WilliTourt/PixPill/Hardware/PCBs/Imgs/EVK V2/IMG_20260525_212544.jpg

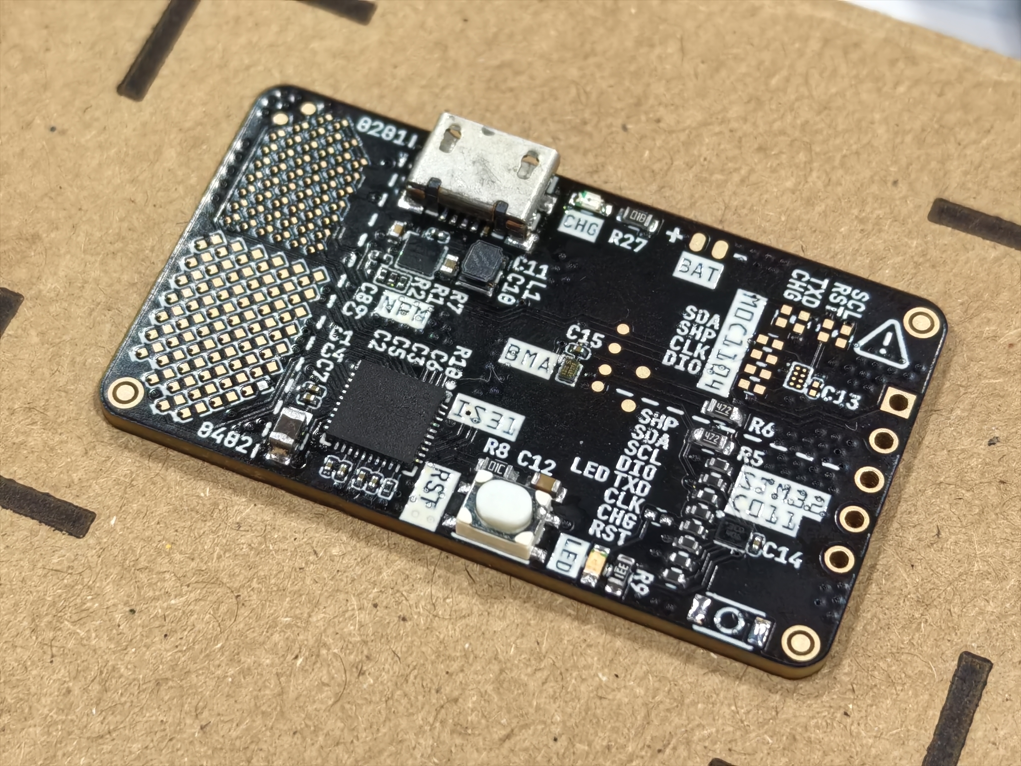
Hardware/PCBs/Imgs/EVK V2/IMG_20260525_212544.jpg
