WilliTourt/PixPill/Hardware/PCBs/Imgs/EVK V2/IMG_20260529_113353.jpg

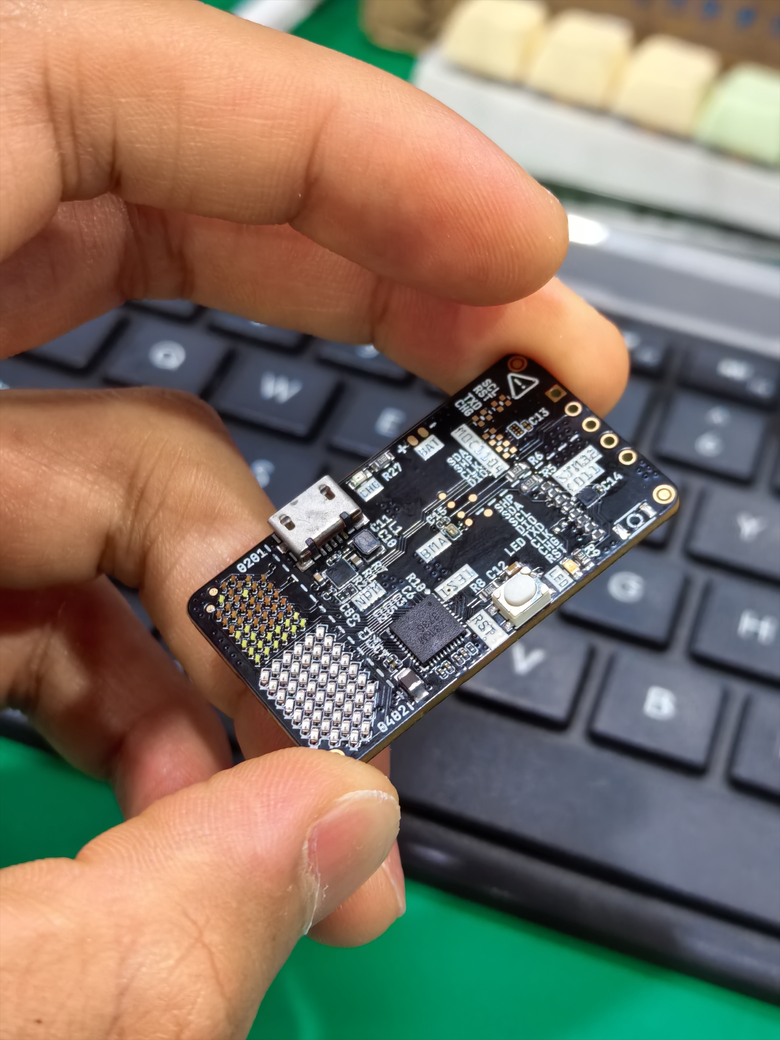
Hardware/PCBs/Imgs/EVK V2/IMG_20260529_113353.jpg
