WilliTourt/PixPill/Hardware/PCBs/Imgs/EVK V2/IMG_20260531_200836.jpg

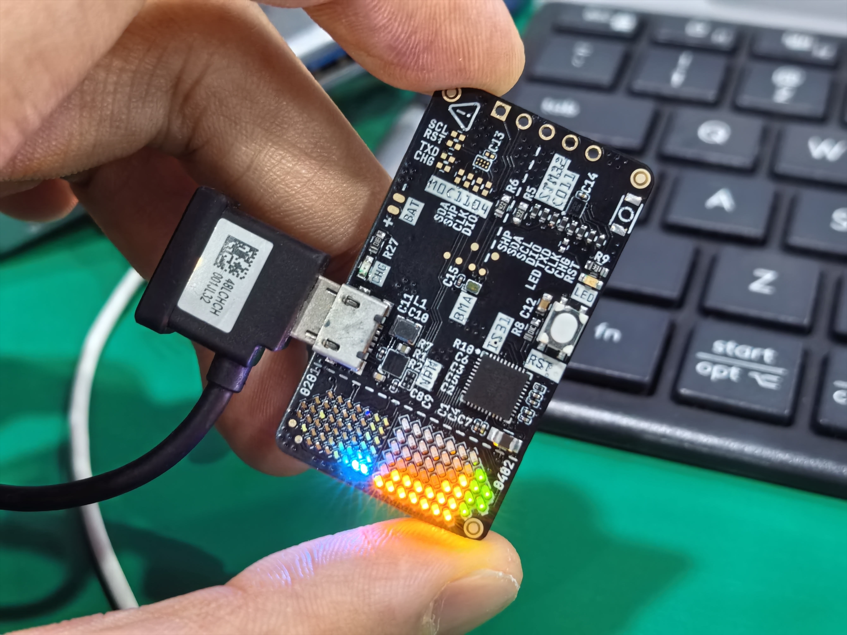
Hardware/PCBs/Imgs/EVK V2/IMG_20260531_200836.jpg
