WilliTourt/PixPill/Hardware/PCBs/Imgs/EVK V2/IMG_20260531_201009.jpg

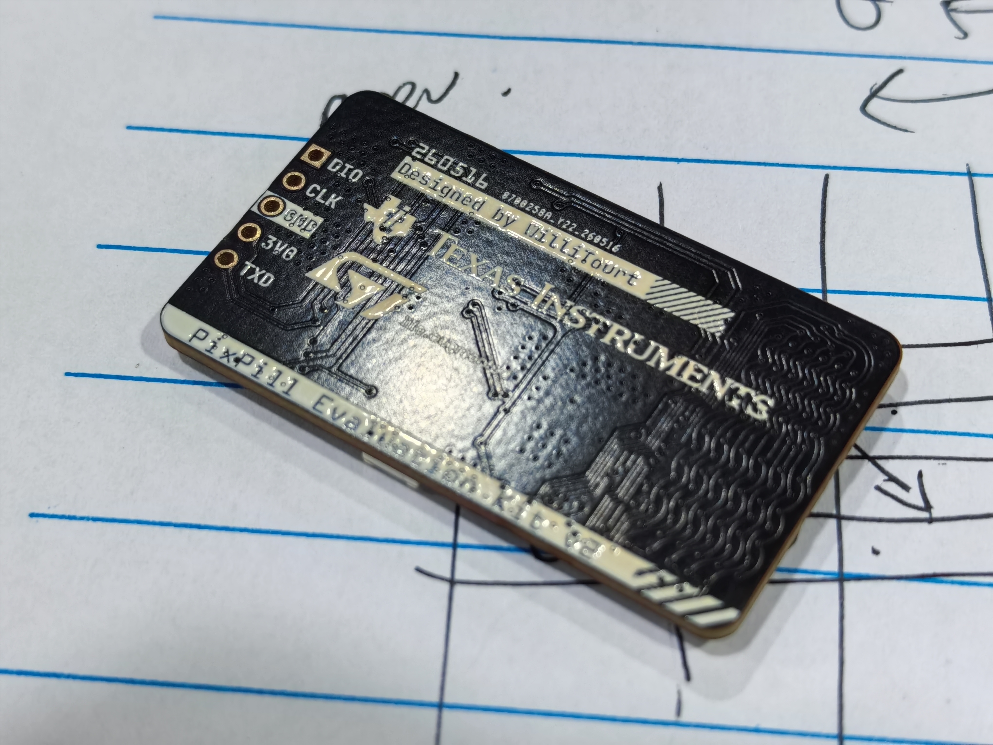
Hardware/PCBs/Imgs/EVK V2/IMG_20260531_201009.jpg
