WilliTourt/PixPill/Hardware/PCBs/Schems and Layout/EVK V2/EVK V2 Bottom.png

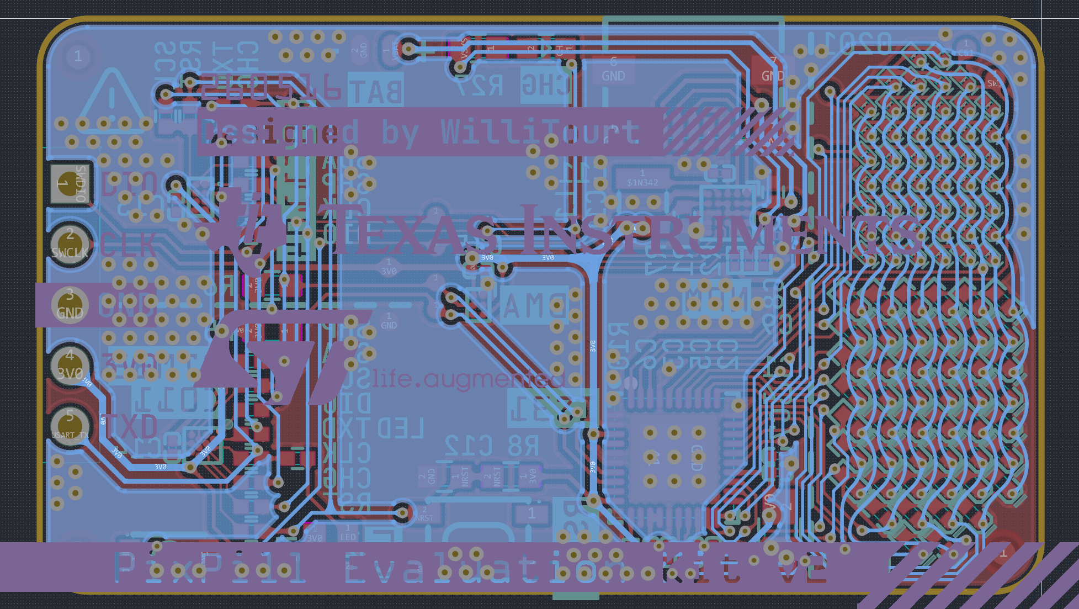
Hardware/PCBs/Schems and Layout/EVK V2/EVK V2 Bottom.png
