WilliTourt/PixPill/Hardware/PCBs/Schems and Layout/EVK V2/IS31.png

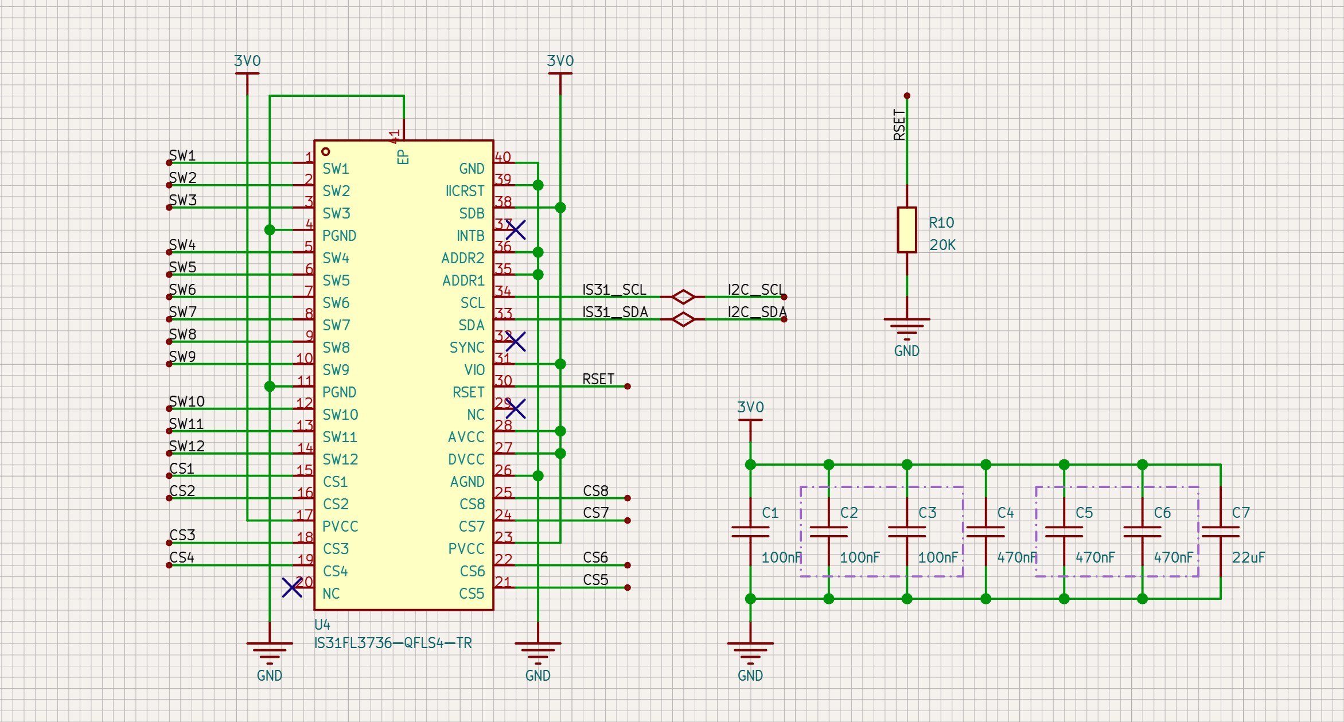
Hardware/PCBs/Schems and Layout/EVK V2/IS31.png
