WilliTourt/PixPill/Hardware/PCBs/Schems and Layout/EVK V2/MCU and BMA.png

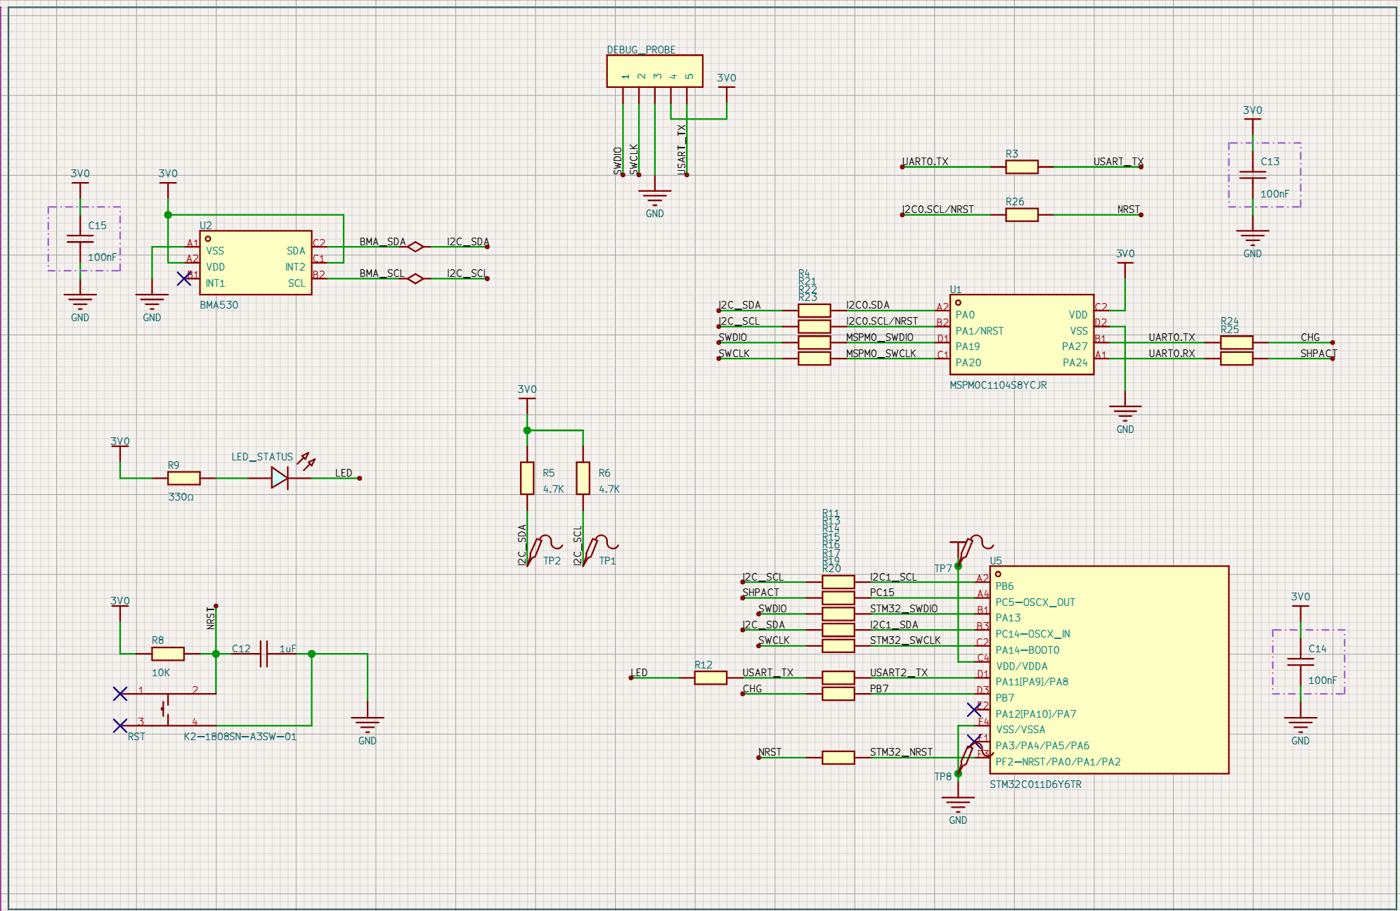
Hardware/PCBs/Schems and Layout/EVK V2/MCU and BMA.png
