WilliTourt/PixPill/Hardware/PCBs/Schems and Layout/Size 000/Size000 Bottom.png

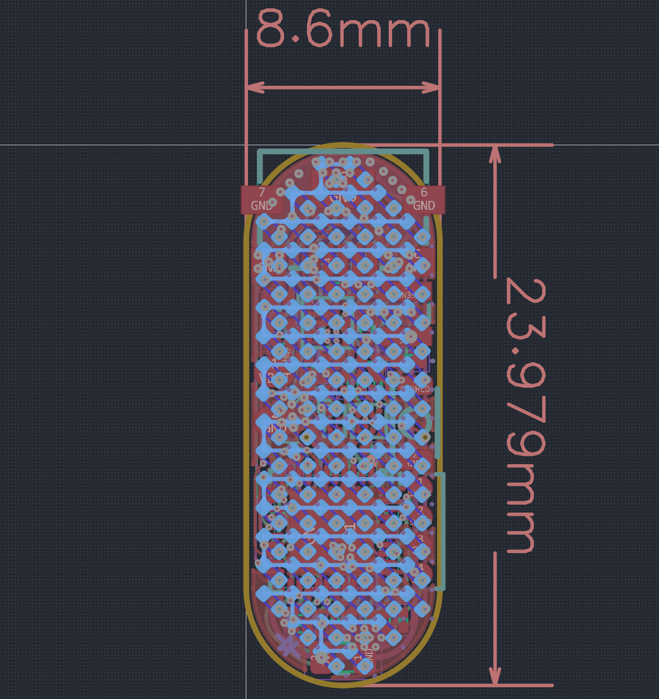
Hardware/PCBs/Schems and Layout/Size 000/Size000 Bottom.png
