WilliTourt/PixPill/Hardware/PCBs/Schems and Layout/Size 000/Size000 Inner1.png

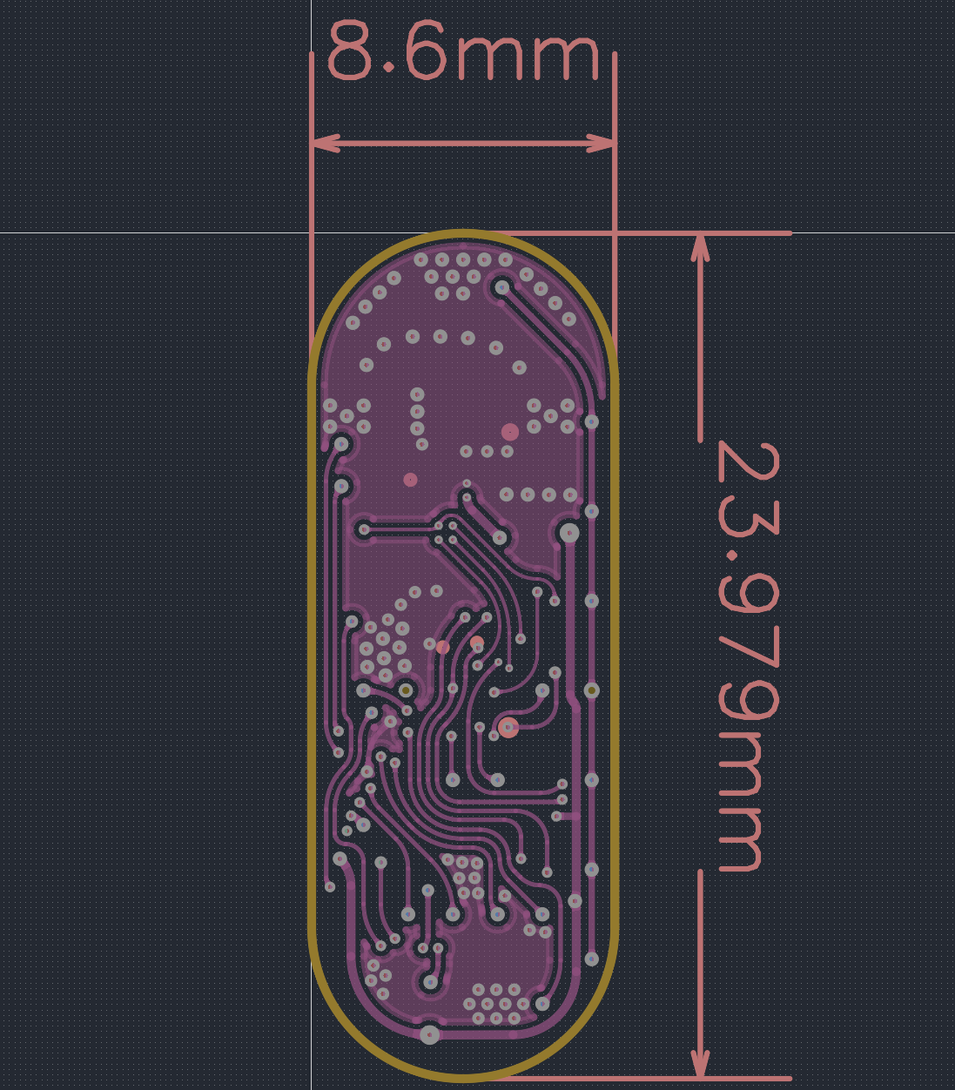
Hardware/PCBs/Schems and Layout/Size 000/Size000 Inner1.png
