WilliTourt/PixPill/Hardware/PCBs/Schems and Layout/Size 000/Size000 Inner2.png

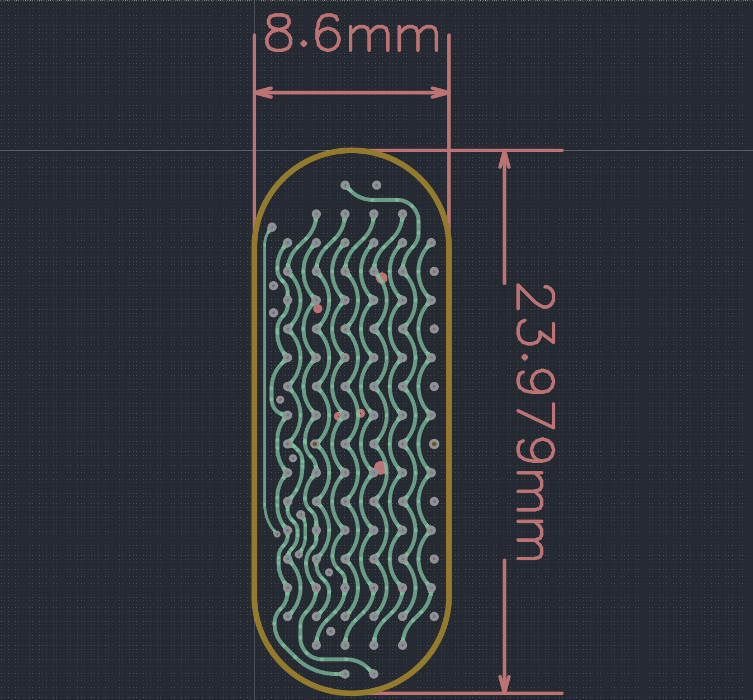
Hardware/PCBs/Schems and Layout/Size 000/Size000 Inner2.png
