WilliTourt/PixPill/Hardware/PCBs/Schems and Layout/Size 000/Size000 Schematic (1).png

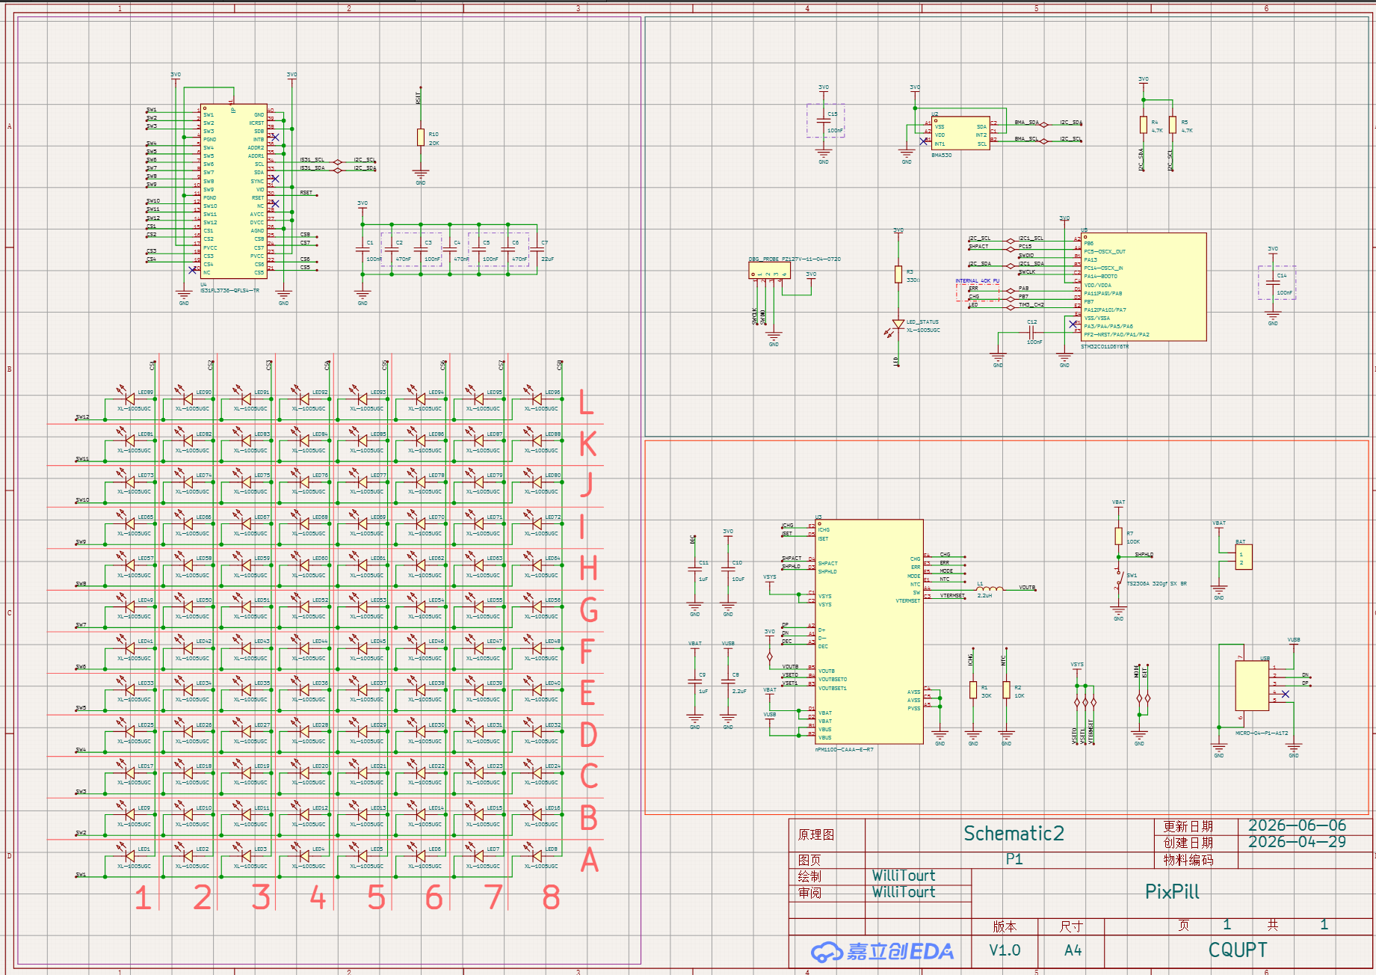
Hardware/PCBs/Schems and Layout/Size 000/Size000 Schematic (1).png
