WilliTourt/PixPill/Hardware/PCBs/Schems and Layout/Size 000/Size000 Top.png

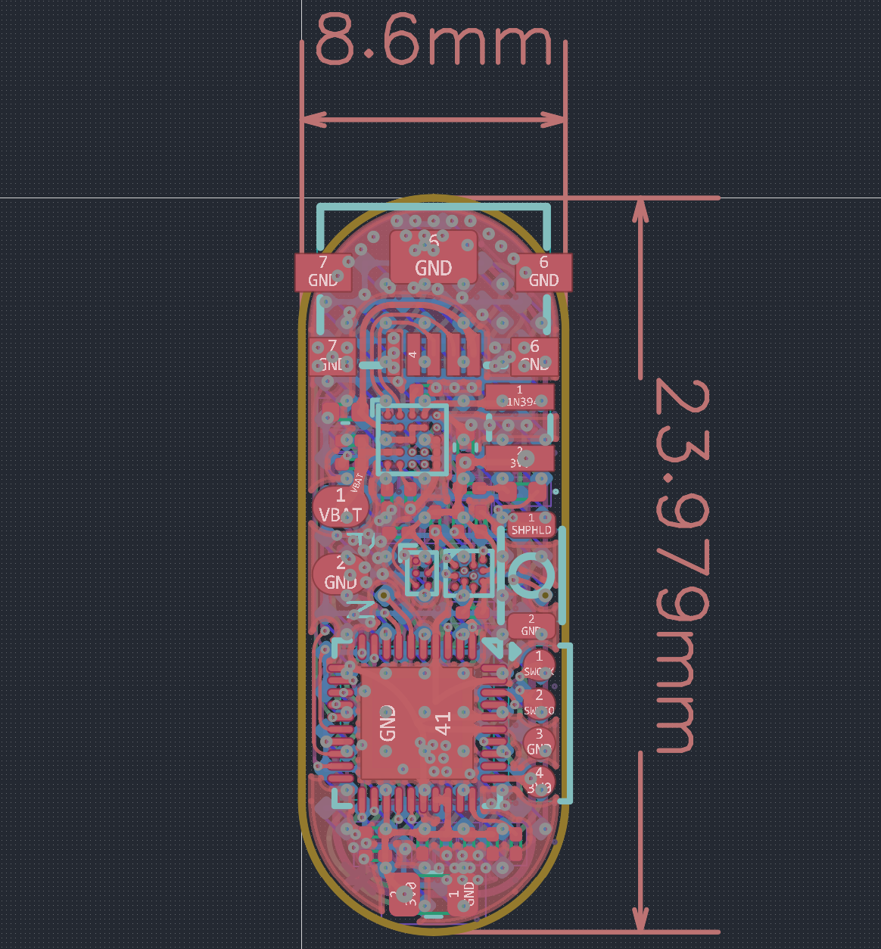
Hardware/PCBs/Schems and Layout/Size 000/Size000 Top.png
