WilliTourt/PixPill/Hardware/PCBs/Schems and Layout/Size 1/Size1 Inner1.png

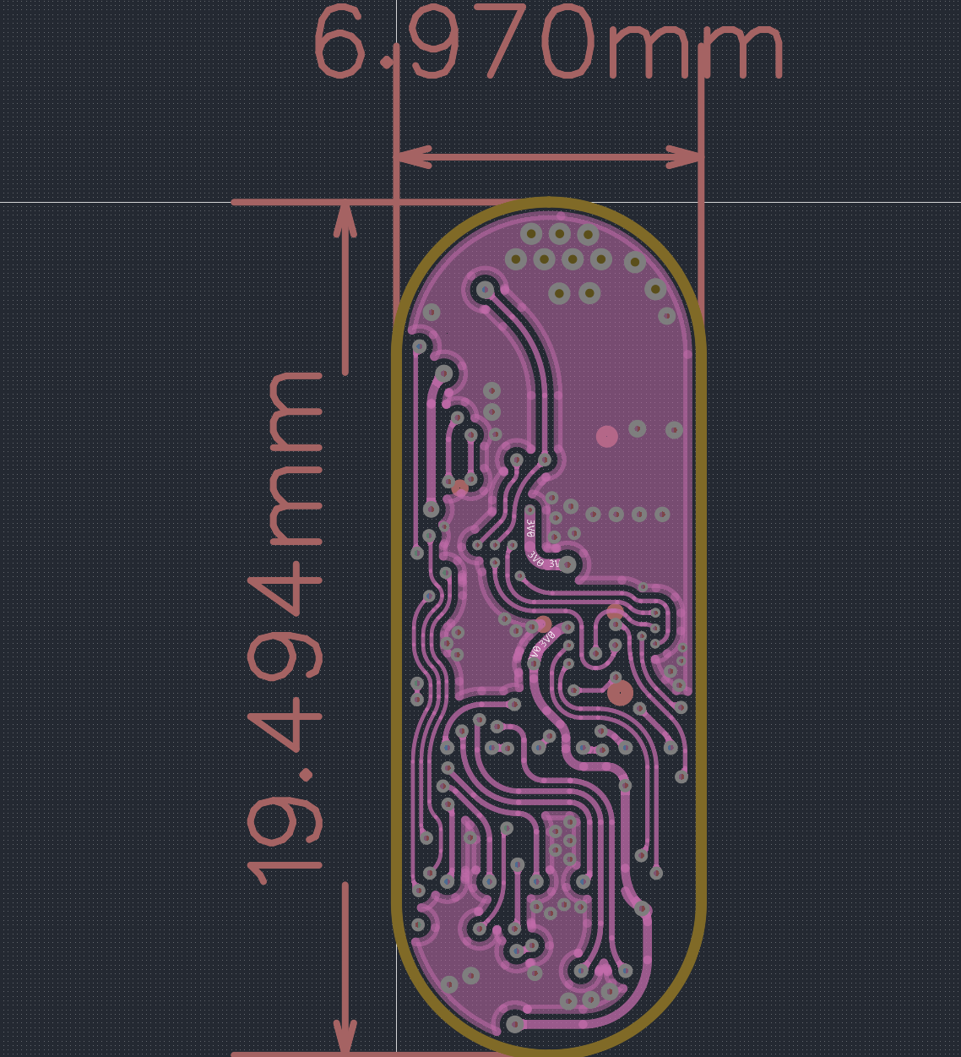
Hardware/PCBs/Schems and Layout/Size 1/Size1 Inner1.png
