WilliTourt/PixPill/Hardware/PCBs/Schems and Layout/Size 1/Size1 Schematic (4).png

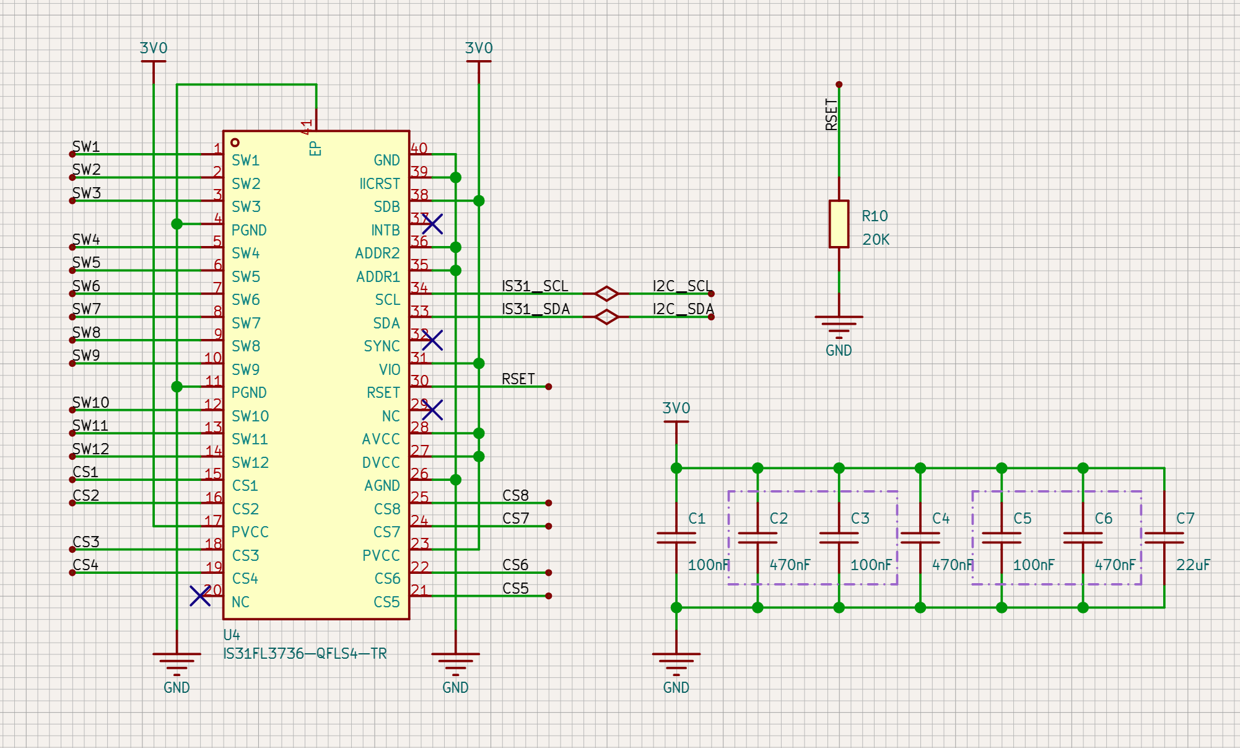
Hardware/PCBs/Schems and Layout/Size 1/Size1 Schematic (4).png
