WilliTourt/PixPill/Hardware/屏幕截图 2026-09-07 174523.png

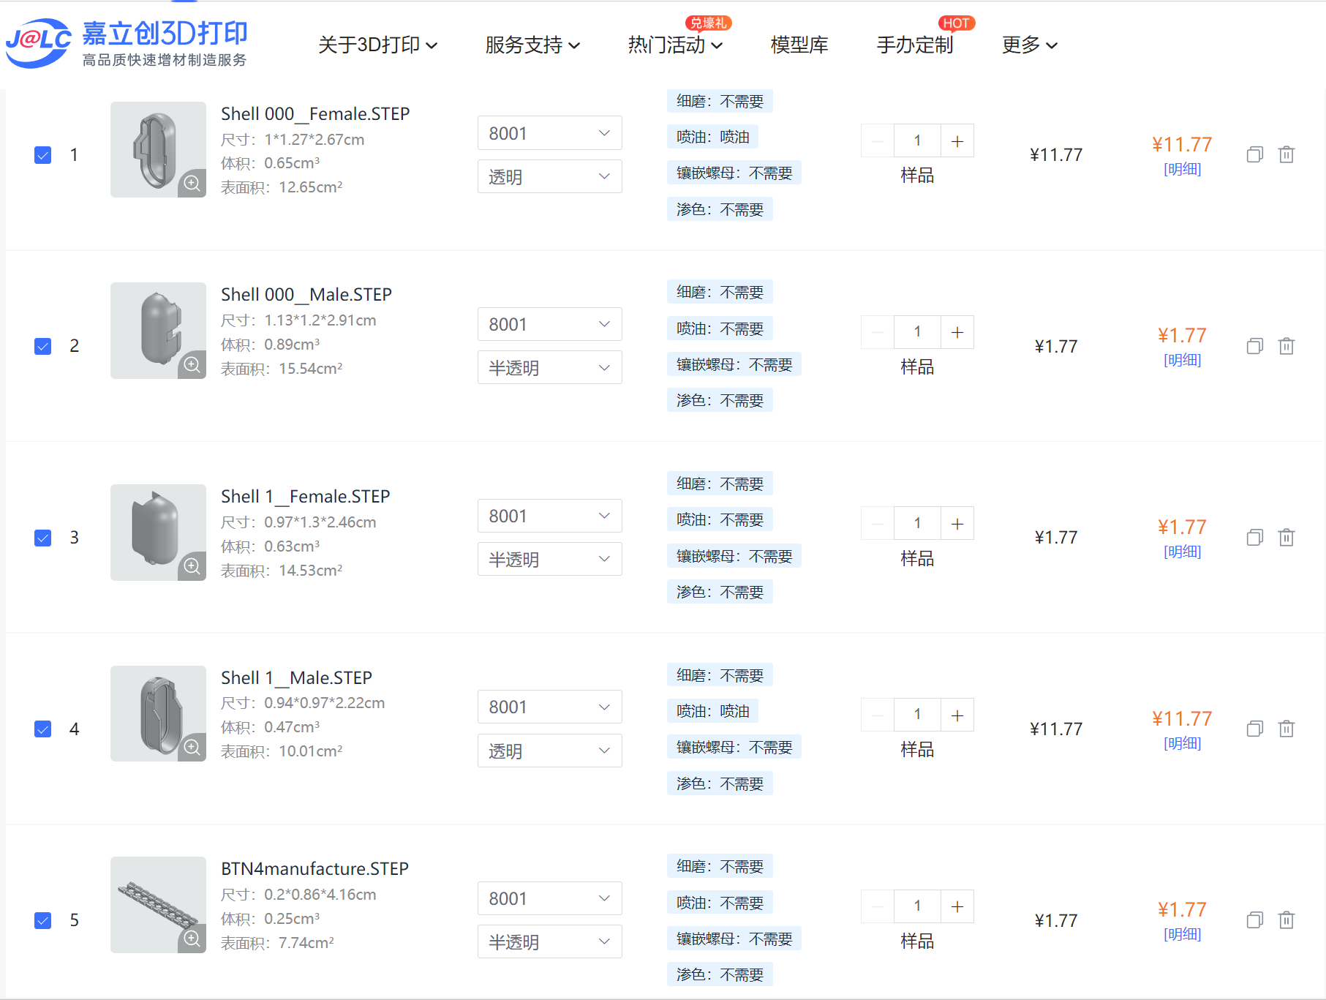
Hardware/屏幕截图 2026-09-07 174523.png
