WilliTourt/PixPill/Hardware/3D Shell/SW/1#/PixPill BTN Attacher 1# recessing tool.SLDPRT

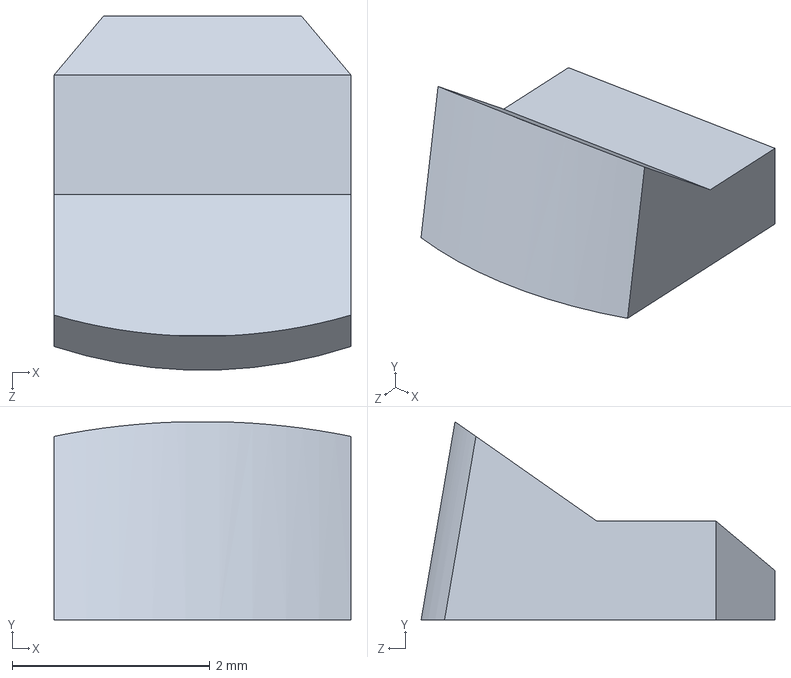
[picture p59: CAD file, 2026-08-11]
Hardware/3D Shell/SW/1#/PixPill BTN Attacher 1# recessing tool.SLDPRT
3.00 x 2.00 x 3.57 mm
