WilliTourt/PixPill/Hardware/3D Shell/SW/1#/battery 08120 recessing tool.SLDPRT

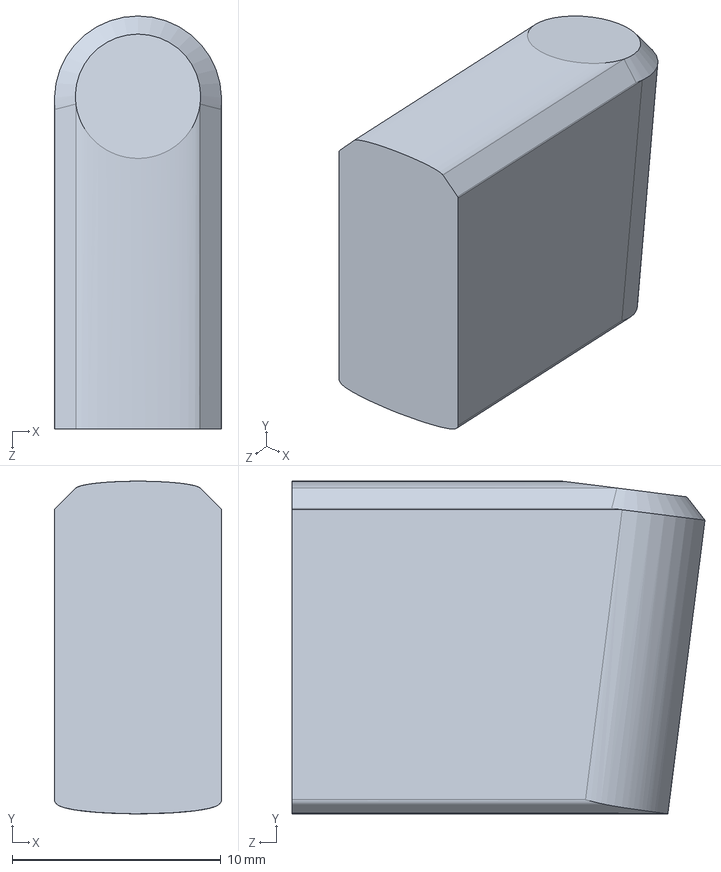
[picture p60: CAD file, 2026-08-11]
Hardware/3D Shell/SW/1#/battery 08120 recessing tool.SLDPRT
8.00 x 15.9 x 19.8 mm
