WilliTourt/PixPill/Hardware/3D Shell/SW/battery 08120 REF.SLDPRT

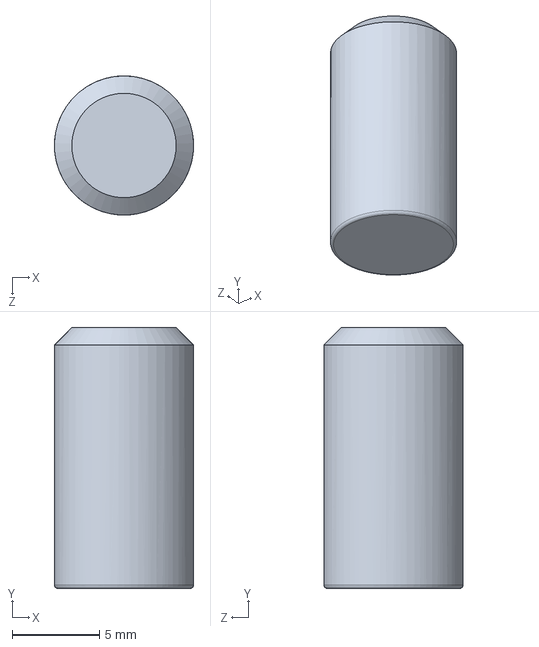
[picture p61: CAD file, 2026-07-14]
Hardware/3D Shell/SW/battery 08120 REF.SLDPRT
8.00 x 15.0 x 8.00 mm
