WilliTourt/PixPill/Software/EIDE Project Folder/PixPill/Components/Inc/pixpill_neighbors_table.h

#ifndef PIXPILL_NEIGHBORS_TABLE_H
#define PIXPILL_NEIGHBORS_TABLE_H

#include <stdint.h>
#include "PIXPILL_VERSION_SELECT.h"

/*** Sandsim led matrix *****************************

         col=0 col=1 col=2 col=3 col=4 col=5
        +-----+-----+-----+-----+-----+-----+
 row=0  |  ×  |  ×  |  A1 |  B1 |  ×  |  ×  |
        +-----+-----+-----+-----+-----+-----+
 row=1  |  ×  |  C1 |  D1 |  E1 |  F1 |  ×  |
        +-----+-----+-----+-----+-----+-----+
 row=2  |  G1 |  H1 |  I1 |  J1 |  K1 |  L1 |
        +-----+-----+-----+-----+-----+-----+
  ...                    ...
        +-----+-----+-----+-----+-----+-----+
 row=16 |  ×  |  G8 |  H8 |  I8 |  J8 |  ×  |
        +-----+-----+-----+-----+-----+-----+
 row=17 |  ×  |  ×  |  K8 |  L8 |  ×  |  ×  |
        +-----+-----+-----+-----+-----+-----+

****************************************************/

// 8-direction clockwise: UP=0, UP-RIGHT=1, RIGHT=2, DOWN-RIGHT=3, DOWN=4, DOWN-LEFT=5, LEFT=6, UP-LEFT=7
#define NEIGHBOR_UP         (uint8_t)0
#define NEIGHBOR_UP_RIGHT   (uint8_t)1
#define NEIGHBOR_RIGHT      (uint8_t)2
#define NEIGHBOR_DOWN_RIGHT (uint8_t)3
#define NEIGHBOR_DOWN       (uint8_t)4
#define NEIGHBOR_DOWN_LEFT  (uint8_t)5
#define NEIGHBOR_LEFT       (uint8_t)6
#define NEIGHBOR_UP_LEFT    (uint8_t)7

// LED INDEX:
// Ln00:         [00][01]
// Ln01:     [02][03][04][05]
// Ln02: [06][07][08][09][10][11]
// Ln03: [12][13][14][15][16][17]
// Ln04: [18][19][20][21][22][23]
// Ln05: [24][25][26][27][28][29]
// Ln06: [30][31][32][33][34][35]
// Ln07: [36][37][38][39][40][41]
// Ln08: [42][43][44][45][46][47]
// Ln09: [48][49][50][51][52][53]
// Ln10: [54][55][56][57][58][59]
// Ln11: [60][61][62][63][64][65]
// Ln12: [66][67][68][69][70][71]
// Ln13: [72][73][74][75][76][77]
// Ln14: [78][79][80][81][82][83]
// Ln15: [84][85][86][87][88][89]
// Ln16:     [90][91][92][93]
// Ln17:         [94][95]

// LED neighbor table: [UP, UR, RIGHT, DR, DOWN, DL, LEFT, UL], number is the LED index, -1 = no neighbor
#ifdef PIXPILL_SIZE_1_CAPSULE

static const int8_t LED_NEIGHBORS[96][8] = {
                                                          {-1,-1,-1,-1,-1,-1,-1,-1}, {-1,-1,-1,-1,-1,-1,-1,-1},
                               {-1,-1,-1,-1,-1,-1,-1,-1}, {-1,-1,-1,-1,-1,-1,-1,-1}, {-1,-1,-1,-1,-1,-1,-1,-1}, {-1,-1,-1,-1,-1,-1,-1,-1}, 
    {-1,-1, 7,13,12,-1,-1,-1}, {-1,-1, 8,14,13,12, 6,-1}, {-1,-1, 9,15,14,13, 7,-1}, {-1,-1,10,16,15,14, 8,-1}, {-1,-1,11,17,16,15, 9,-1}, {-1,-1,-1,-1,17,16,10,-1},   // Ln02: [G1][H1][I1][J1][K1][L1]
    { 6, 7,13,19,18,-1,-1,-1}, { 7, 8,14,20,19,18,12, 6}, { 8, 9,15,21,20,19,13, 7}, { 9,10,16,22,21,20,14, 8}, {10,11,17,23,22,21,15, 9}, {11,-1,-1,-1,23,22,16,10},   // Ln03: [A2][B2][C2][D2][E2][F2]
    {12,13,19,25,24,-1,-1,-1}, {13,14,20,26,25,24,18,12}, {14,15,21,27,26,25,19,13}, {15,16,22,28,27,26,20,14}, {16,17,23,29,28,27,21,15}, {17,-1,-1,-1,29,28,22,16},   // Ln04: [G2][H2][I2][J2][K2][L2]
    {18,19,25,31,30,-1,-1,-1}, {19,20,26,32,31,30,24,18}, {20,21,27,33,32,31,25,19}, {21,22,28,34,33,32,26,20}, {22,23,29,35,34,33,27,21}, {23,-1,-1,-1,35,34,28,22},   // Ln05: [A3][B3][C3][D3][E3][F3]
    {24,25,31,37,36,-1,-1,-1}, {25,26,32,38,37,36,30,24}, {26,27,33,39,38,37,31,25}, {27,28,34,40,39,38,32,26}, {28,29,35,41,40,39,33,27}, {29,-1,-1,-1,41,40,34,28},   // Ln06: [G3][H3][I3][J3][K3][L3]
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
    54, 49, 44, 39, 34, 29,
    60, 55, 50, 45, 40, 35,
    66, 61, 56, 51, 46, 41,
    72, 67, 62, 57, 52, 47,
    78, 73, 68, 63, 58, 53,
    84, 79, 74, 69, 64, 59,
    85, 80, 75, 70, 65,
    90, 86, 81, 76, 71,
    91, 87, 82, 77,
    94, 92, 88, 83,
    95, 93, 89
};

#endif
