WilliTourt/PixPill/Software/EIDE Project Folder/PixPill/Components/Src/inv_sqrt_table.cpp

#include "inv_sqrt_table.h"

const float inv_sqrt_table[INV_SQRT_TABLE_SIZE] = {
    20.000000f, 11.313708f, 8.000000f, 6.531973f,
    5.656854f, 5.059644f, 4.618802f, 4.276180f,
    4.000000f, 3.771236f, 3.577709f, 3.411211f,
    3.265986f, 3.137858f, 3.023716f, 2.921187f,
    2.828427f, 2.743977f, 2.666667f, 2.595543f,
    2.529822f, 2.468854f, 2.412091f, 2.359071f,
    2.309401f, 2.262742f, 2.218801f, 2.177324f,
    2.138090f, 2.100903f, 2.065591f, 2.032002f,
    2.000000f, 1.969464f, 1.940285f, 1.912366f,
    1.885618f, 1.859962f, 1.835326f, 1.811643f,
    1.788854f, 1.766904f, 1.745743f, 1.725324f,
    1.705606f, 1.686548f, 1.668115f, 1.650274f,
    1.632993f, 1.616244f, 1.600000f, 1.584236f,
    1.568929f, 1.554057f, 1.539601f, 1.525540f,
    1.511858f, 1.498537f, 1.485563f, 1.472919f,
    1.460593f, 1.448572f, 1.436842f, 1.425393f,
    1.414214f, 1.403293f, 1.392621f, 1.382189f,
    1.371989f, 1.362010f, 1.352247f, 1.342690f,
    1.333333f, 1.324169f, 1.315192f, 1.306395f,
    1.297771f, 1.289317f, 1.281025f, 1.272892f,
    1.264911f, 1.257079f, 1.249390f, 1.241841f,
    1.234427f, 1.227144f, 1.219989f, 1.212957f,
    1.206045f, 1.199251f, 1.192570f, 1.185999f,
    1.179536f, 1.173177f, 1.166920f, 1.160762f,
    1.154701f, 1.148733f, 1.142857f, 1.137070f,
    1.131371f, 1.125756f, 1.120224f, 1.114773f,
    1.109400f, 1.104105f, 1.098885f, 1.093737f,
    1.088662f, 1.083657f, 1.078720f, 1.073850f,
    1.069045f, 1.064304f, 1.059626f, 1.055009f,
    1.050451f, 1.045953f, 1.041511f, 1.037126f,
    1.032796f, 1.028519f, 1.024295f, 1.020123f,
    1.016001f, 1.011929f, 1.007905f, 1.003929f,
    1.000000f, 0.996116f, 0.992278f, 0.988483f,
    0.984732f, 0.981023f, 0.977356f, 0.973729f,
    0.970143f, 0.966595f, 0.963087f, 0.959616f,
    0.956183f, 0.952786f, 0.949425f, 0.946100f,
    0.942809f, 0.939552f, 0.936329f, 0.933139f,
    0.929981f, 0.926855f, 0.923760f, 0.920697f,
    0.917663f, 0.914659f, 0.911685f, 0.908739f,
    0.905822f, 0.902932f, 0.900070f, 0.897235f,
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
};

float inv_sqrt_lookup(float dist_sq) {
    int idx = (int)(dist_sq * INV_SQRT_TABLE_SCALE);
    if (idx < 0) idx = 0;
    if (idx >= INV_SQRT_TABLE_SIZE) idx = INV_SQRT_TABLE_SIZE - 1;
    return inv_sqrt_table[idx];
}
